derekdvleung/totblocks/3mf/connectors/chlorite-connector.3mf

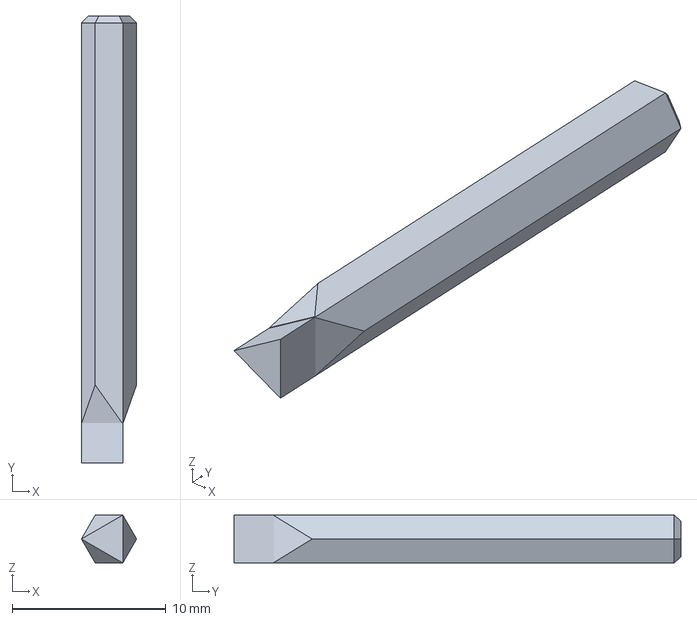
[picture p15: CAD file, 2022-05-19]
3mf/connectors/chlorite-connector.3mf
3.60 x 29.1 x 3.12 mm
