derekdvleung/totblocks/3mf/oblock/oblock-m2-minus.3mf

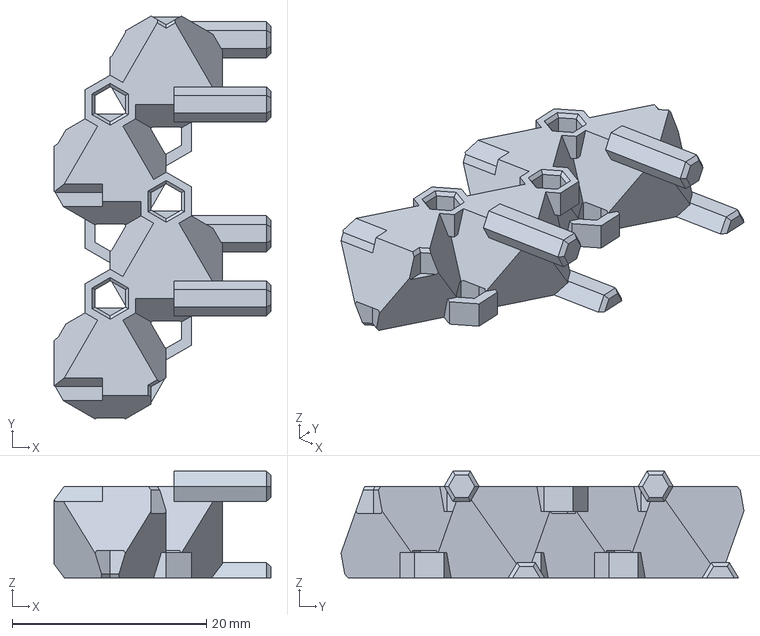
[picture p16: CAD file, 2022-04-24]
3mf/oblock/oblock-m2-minus.3mf
22.3 x 41.5 x 11.0 mm
