derekdvleung/totblocks/stl/dual/tblock-n1-minus-dual-0.stl

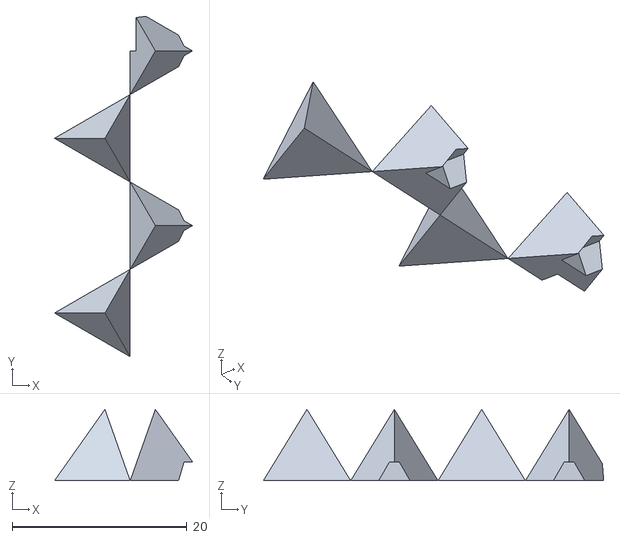
[picture p17: CAD file, 2021-08-20]
stl/dual/tblock-n1-minus-dual-0.stl
15.8 x 39.0 x 8.16
