derekdvleung/totblocks/stl/oblock/oblock-support-enforcer.stl

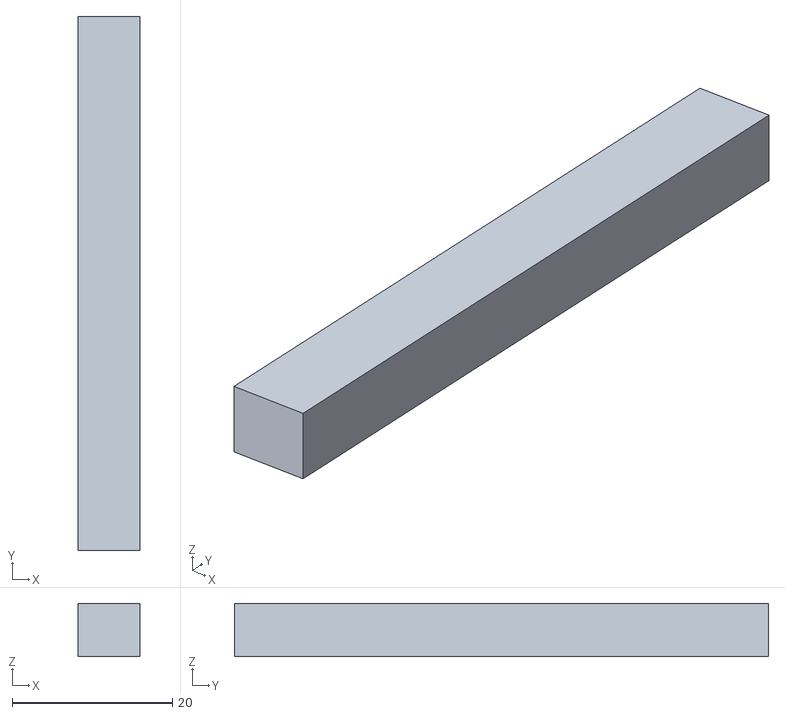
[picture p18: CAD file, 2021-08-20]
stl/oblock/oblock-support-enforcer.stl
7.72 x 66.7 x 6.66
