derekdvleung/totblocks/3mf/connectors/mica-connector.3mf

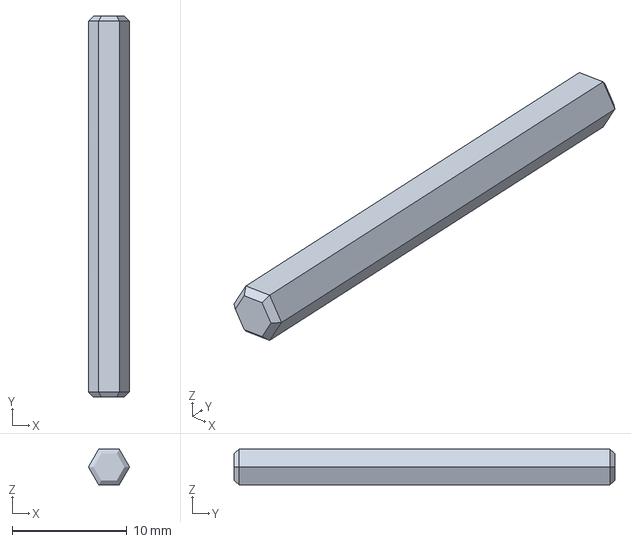
[picture p19: CAD file, 2022-04-24]
3mf/connectors/mica-connector.3mf
3.60 x 33.2 x 3.12 mm
