derekdvleung/totblocks/3mf/oblock/single-octahedron-clips.3mf

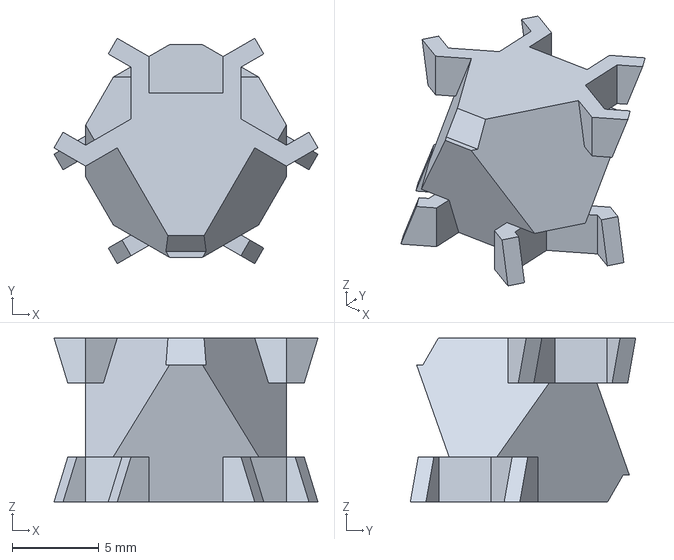
[picture p20: CAD file, 2022-04-24]
3mf/oblock/single-octahedron-clips.3mf
15.2 x 13.0 x 9.43 mm
