derekdvleung/totblocks/3mf/tblock/tblock-n3-minus.3mf

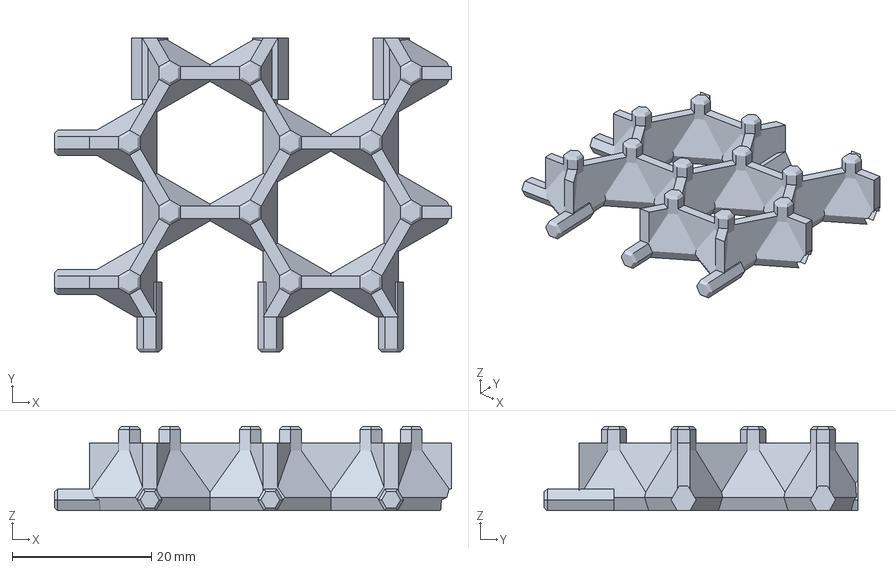
[picture p21: CAD file, 2022-04-24]
3mf/tblock/tblock-n3-minus.3mf
57.0 x 45.0 x 12.1 mm
