derekdvleung/totblocks/stl/dual/tblock-n1-plus-dual-1.stl

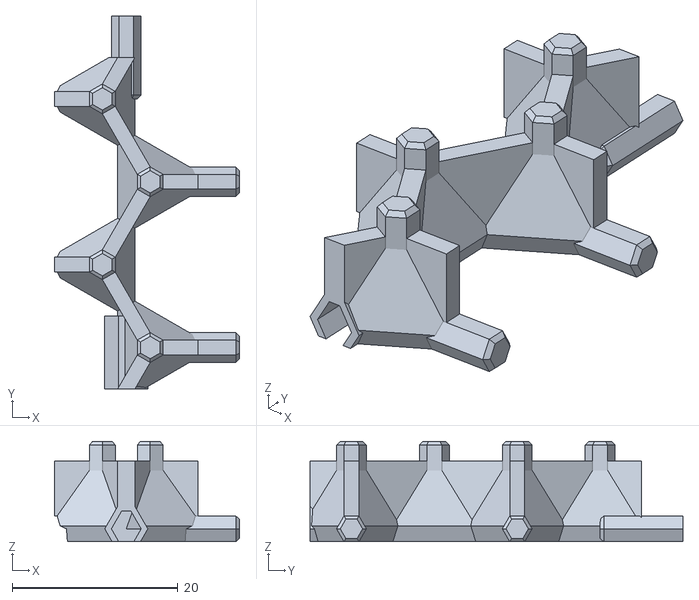
[picture p22: CAD file, 2021-08-20]
stl/dual/tblock-n1-plus-dual-1.stl
22.3 x 45.0 x 12.1
