derekdvleung/totblocks/3mf/oblock/oblock-m8-minus.3mf

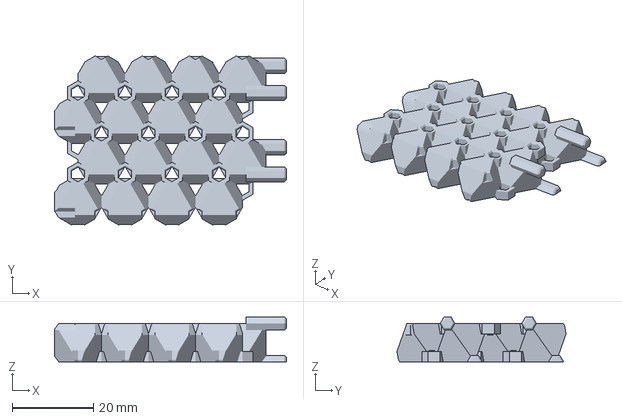
[picture p23: CAD file, 2022-04-24]
3mf/oblock/oblock-m8-minus.3mf
57.0 x 41.5 x 11.0 mm
