derekdvleung/totblocks/3mf/oblock/oblock-m3-plus.3mf

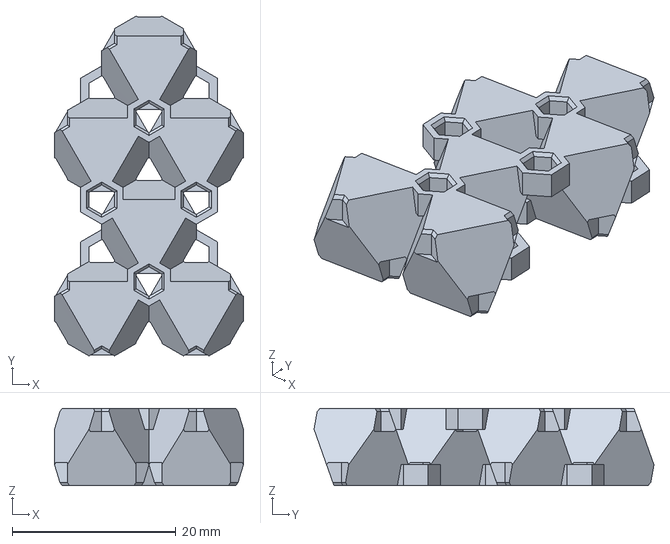
[picture p24: CAD file, 2022-04-24]
3mf/oblock/oblock-m3-plus.3mf
23.1 x 41.5 x 9.43 mm
