derekdvleung/totblocks/stl/dual/tblock-n1-minus-dual-1.stl

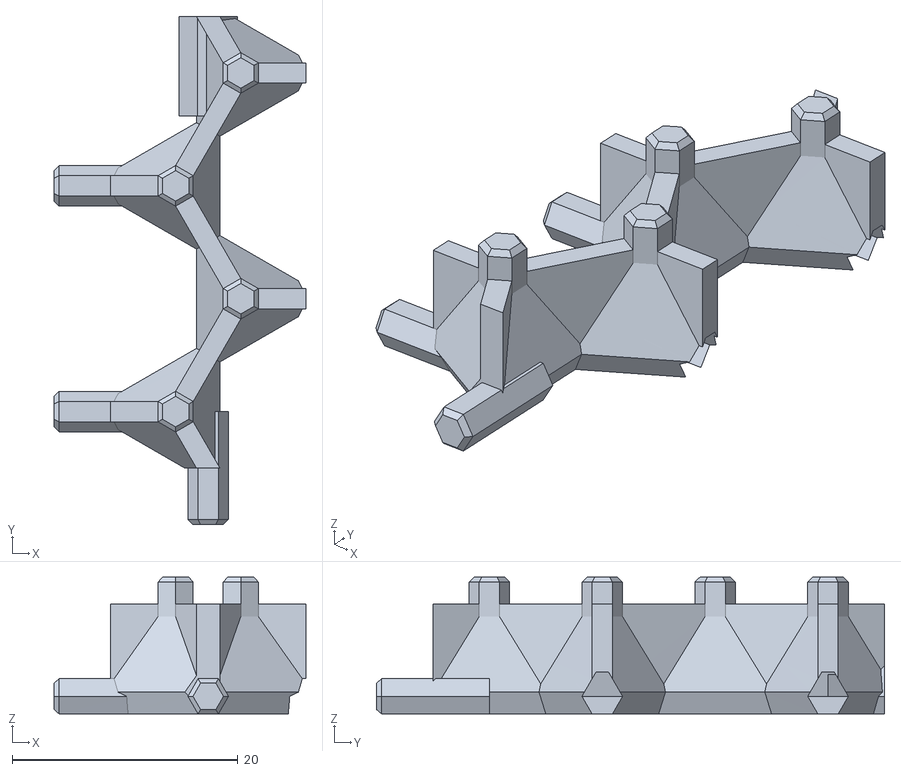
[picture p25: CAD file, 2021-08-20]
stl/dual/tblock-n1-minus-dual-1.stl
22.3 x 45.0 x 12.1
