derekdvleung/totblocks/3mf/oblock/single-octahedron.3mf

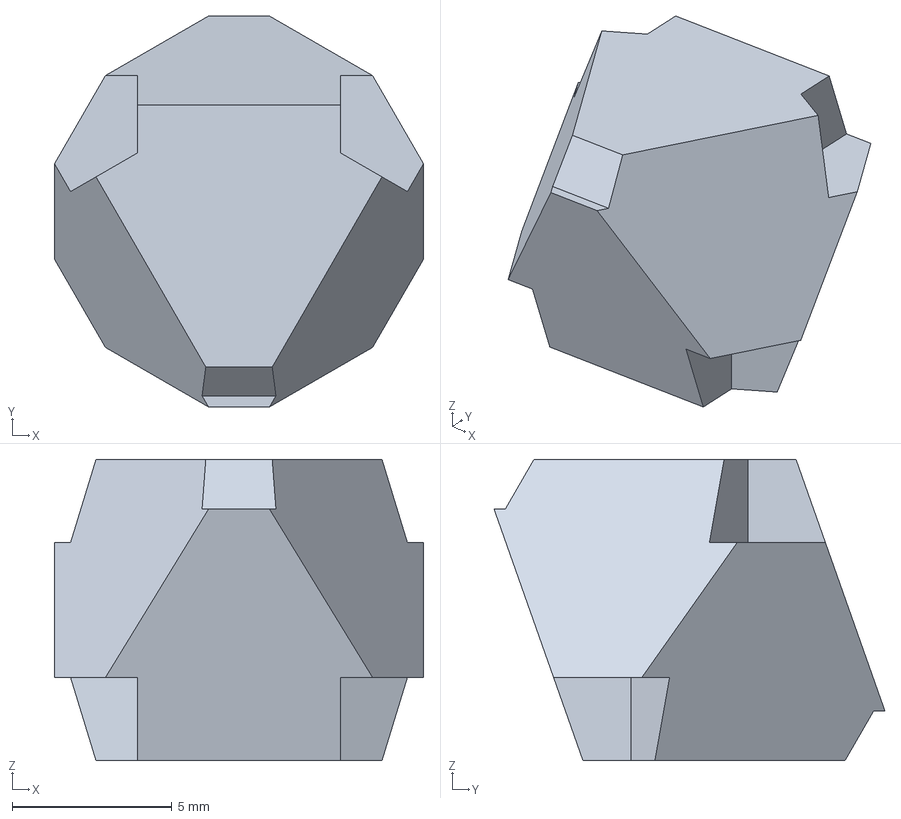
[picture p26: CAD file, 2022-04-24]
3mf/oblock/single-octahedron.3mf
11.5 x 12.2 x 9.43 mm
